ouchitaikoproject/OuchiTaikoProject/.pcb/Screenshot_2026-03-26_at_3.57.48_PM.webp

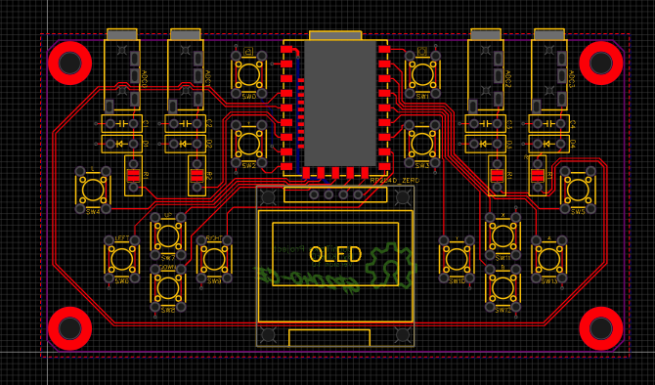
.pcb/Screenshot_2026-03-26_at_3.57.48_PM.webp
