ouchitaikoproject/OuchiTaikoProject/.pcb/Screenshot_2026-03-26_at_3.58.21_PM.webp

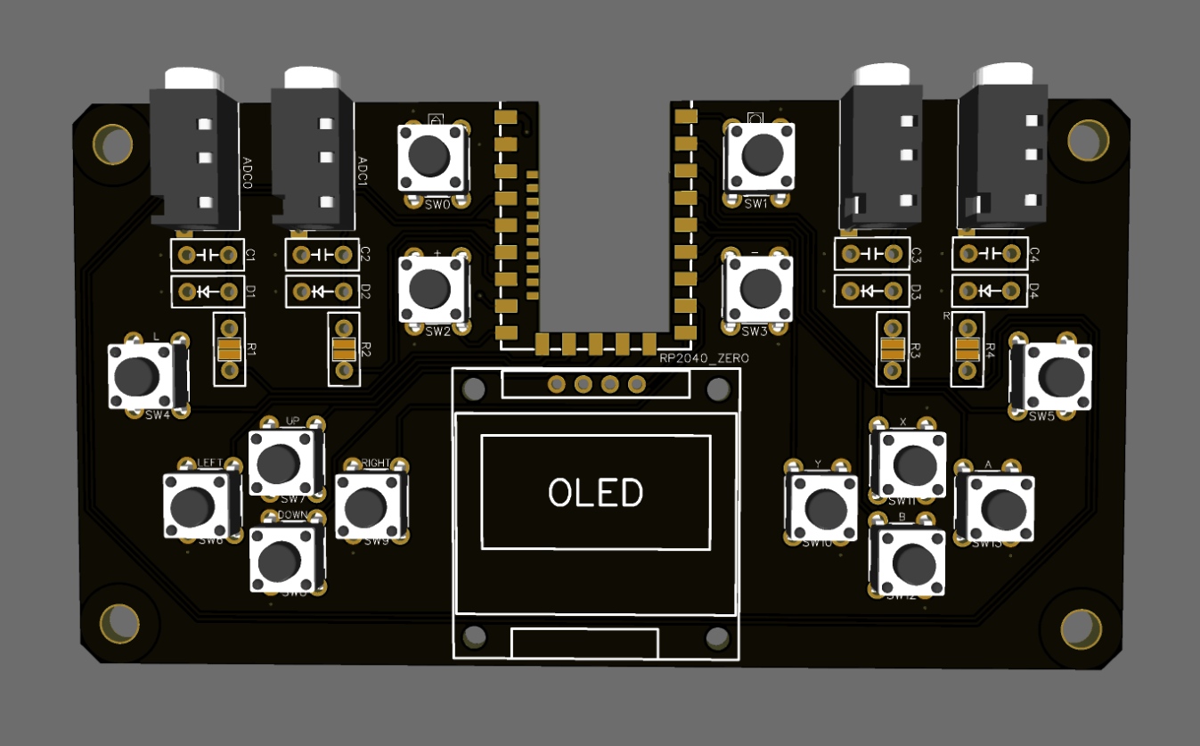
.pcb/Screenshot_2026-03-26_at_3.58.21_PM.webp
