ouchitaikoproject/OuchiTaikoProject/include/PS4AuthConfiguration.h

#ifndef PS4AUTHCONFIGURATION_H_
#define PS4AUTHCONFIGURATION_H_

#include "utils/PS4AuthProvider.h"

namespace OuchiTaiko::Config::PS4Auth {

const Utils::PS4AuthProvider::Config config = {.enabled = false,       // Enabled
                                               .serial = {},           // Serial
                                               .signature = {},        // Signature
                                               .key_pem = "pem()pem"}; // Pem

} // namespace OuchiTaiko::Config::PS4Auth

#endif // PS4AUTHCONFIGURATION_H_
